topolittle/sensor-display/MECHA/PNG/Back.jpg

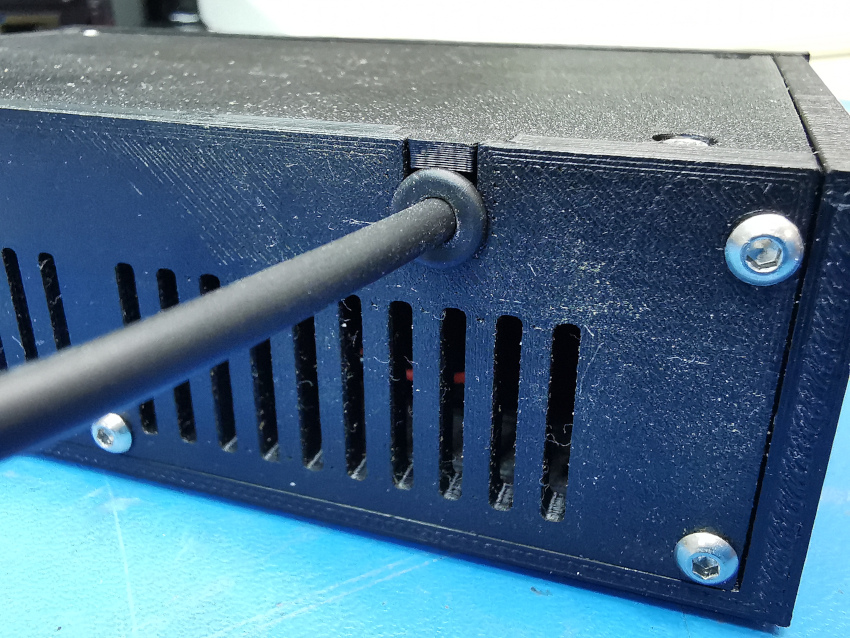
MECHA/PNG/Back.jpg
