topolittle/sensor-display/MECHA/PNG/Front.png

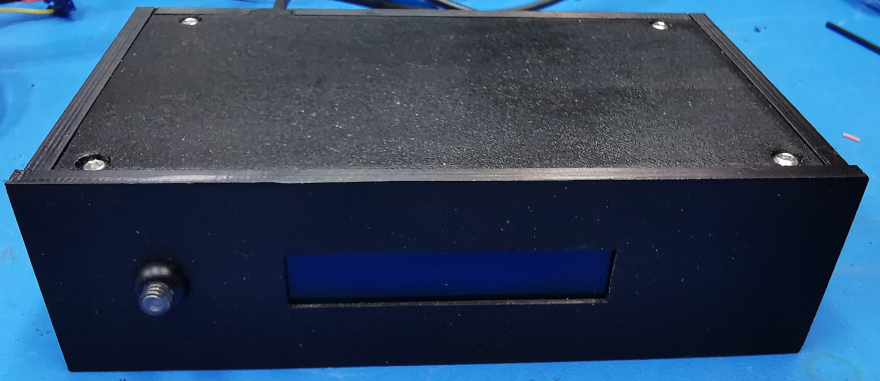
MECHA/PNG/Front.png
