topolittle/sensor-display/MECHA/PNG/Top_panel.PNG

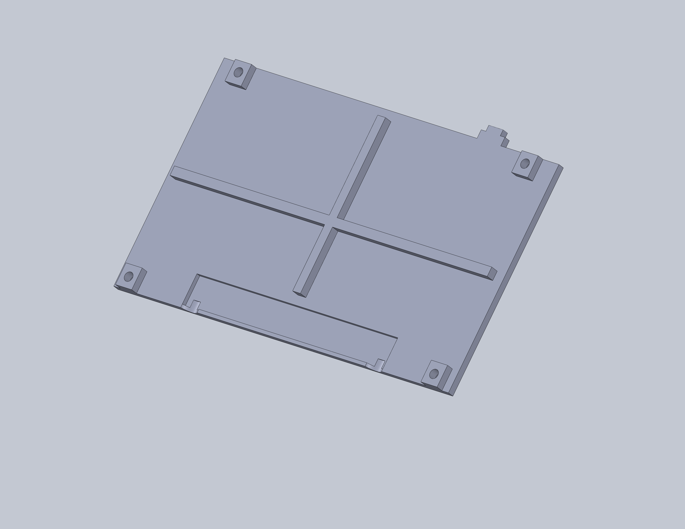
MECHA/PNG/Top_panel.PNG
