topolittle/sensor-display/MECHA/SOLIDWORKS/Complete_Unit_closed.PNG

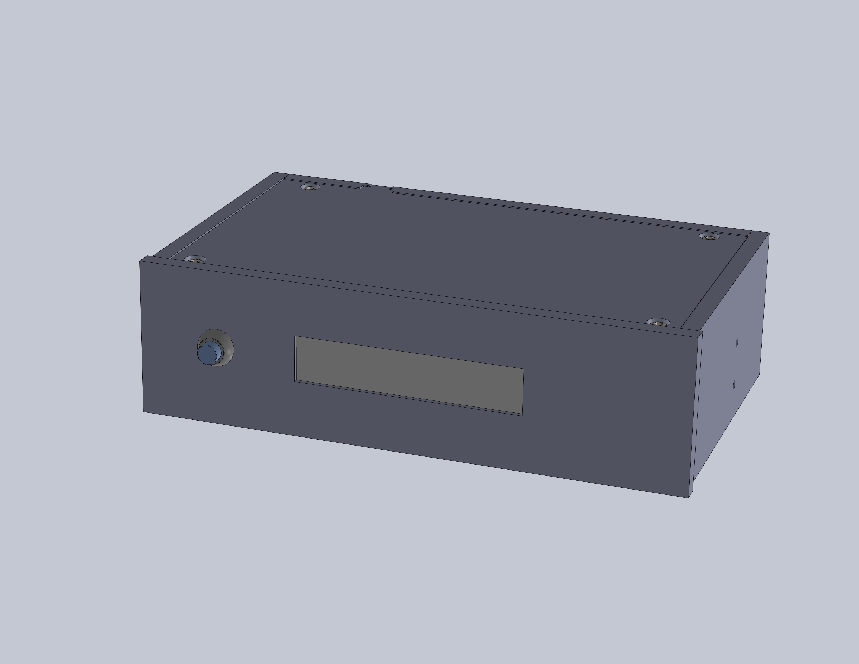
MECHA/SOLIDWORKS/Complete_Unit_closed.PNG
