topolittle/sensor-display/MECHA/PNG/Inside_wiring.PNG

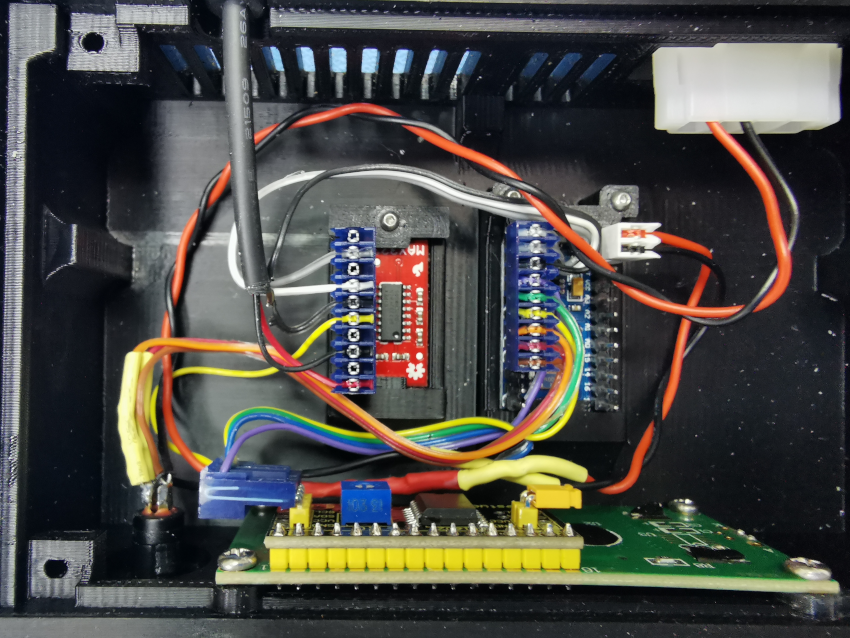
MECHA/PNG/Inside_wiring.PNG
